wikipoz000-netizen/MIDI-Controller-with-gesture-steering/pictures./archutektura_systemu.png

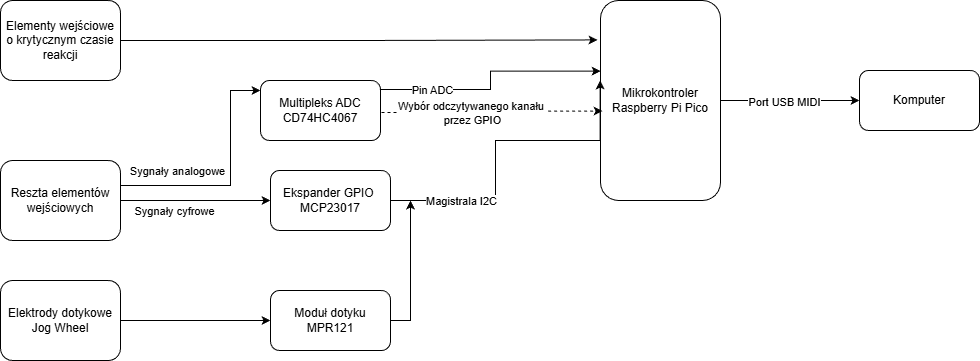
pictures./archutektura_systemu.png
