wikipoz000-netizen/MIDI-Controller-with-gesture-steering/3D models/Jog.step

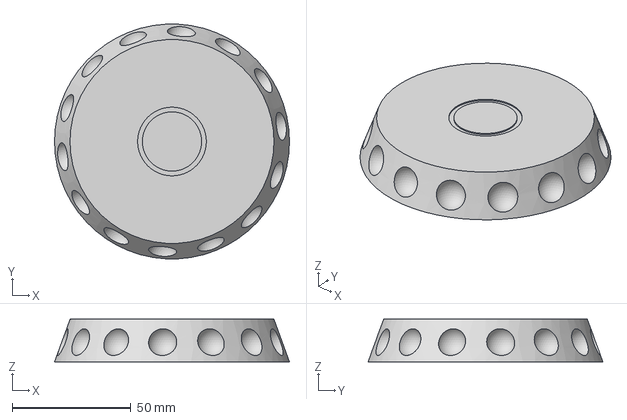
[picture p22: CAD file, 2026-02-17]
3D models/Jog.step
99.2 x 99.0 x 18.0 mm
