wikipoz000-netizen/MIDI-Controller-with-gesture-steering/3D models/play-pause-Body.step

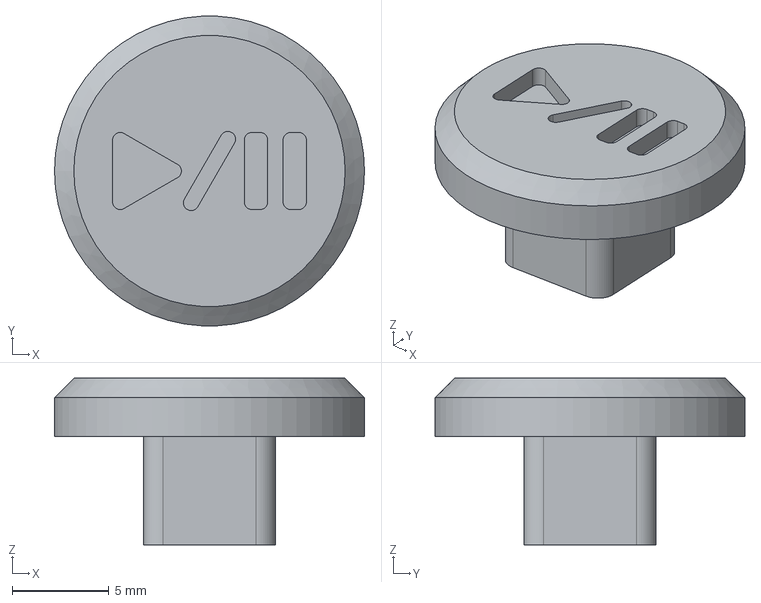
[picture p23: CAD file, 2026-02-17]
3D models/play-pause-Body.step
16.0 x 16.0 x 8.60 mm
